Tonikiller10000/EEPROM_PROGRAMER/EEPROM_PROGRAMER_V3.0/EEPROM_PROGRAMER_V3.0.kicad_sch

## KiCad design EEPROM_PROGRAMER_V3.0/EEPROM_PROGRAMER_V3.0.kicad_sch (2024-02-26, an earlier design)

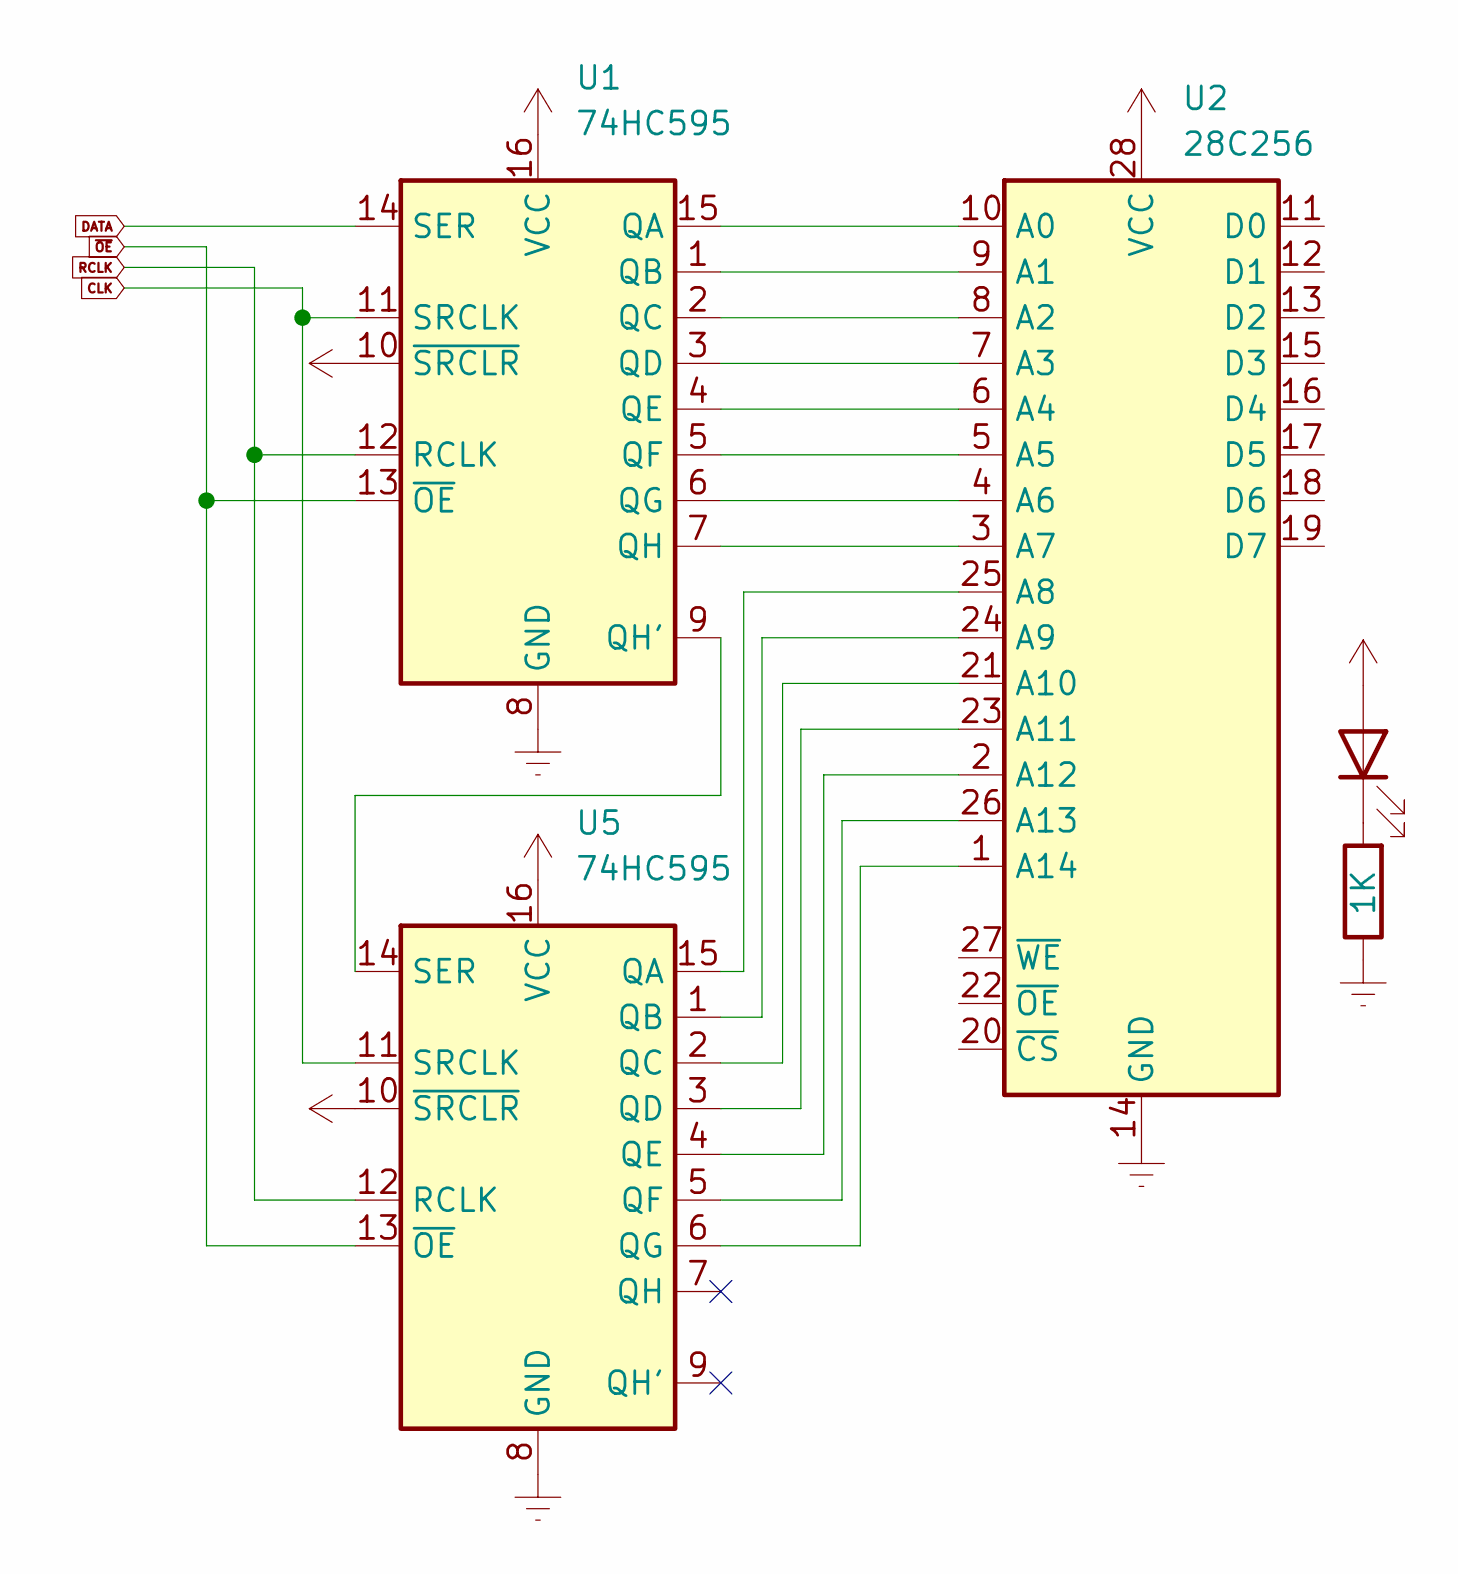
[picture p5: schematic EEPROM_PROGRAMER_V3.0.kicad_sch]

Parts:
1K1: 1K
D1: LED
U1, U5: 74HC595; SOIC-16_3.9x9.9mm_P1.27mm
U2: 28C256

Connections:
CLK: U1.11 (SRCLK), U5.11 (SRCLK)
DATA: U1.14 (SER)
Earth: 1K1.1, U1.8 (GND), U2.14 (GND), U5.8 (GND)
unnamed: 1K1.2, D1.1 (K)
unnamed: U1.1 (QB), U2.9 (A1)
unnamed: U1.2 (QC), U2.8 (A2)
unnamed: U1.3 (QD), U2.7 (A3)
unnamed: U1.4 (QE), U2.6 (A4)
unnamed: U1.5 (QF), U2.5 (A5)
unnamed: U1.6 (QG), U2.4 (A6)
unnamed: U1.7 (QH), U2.3 (A7)
unnamed: U1.9 (QH'), U5.14 (SER)
unnamed: U1.15 (QA), U2.10 (A0)
unnamed: U2.1 (A14), U5.6 (QG)
unnamed: U2.2 (A12), U5.4 (QE)
unnamed: U2.21 (A10), U5.2 (QC)
unnamed: U2.23 (A11), U5.3 (QD)
unnamed: U2.24 (A9), U5.1 (QB)
unnamed: U2.25 (A8), U5.15 (QA)
unnamed: U2.26 (A13), U5.5 (QF)
RCLK: U1.12 (RCLK), U5.12 (RCLK)
VCC: D1.2 (A), U1.10 (~SRCLR), U1.16 (VCC), U2.28 (VCC), U5.10 (~SRCLR), U5.16 (VCC)
~OE: U1.13 (~OE), U5.13 (~OE)
